vladimirgamalyan/imalive/include/config.example.h

#pragma once

// Copy this file to config.h and fill in your values.
// config.h is gitignored and must never be committed (see .gitignore / ADR-0003).

// --- WiFi ---
#define WIFI_SSID      "your-wifi-ssid"
#define WIFI_PASSWORD  "your-wifi-password"

// --- Telegram ---
// Bot token from @BotFather.
#define TG_BOT_TOKEN   "123456789:ABCdefGhIJKlmNoPQRstuVWxyz"
// Destination chat: a personal chat (positive numeric id) or a channel
// ("-100..." or "@channel"). For a channel, add the bot as an administrator
// with post permission. Prefer the numeric "-100..." form: a "@channel" username
// resolves only while the channel is public, and making it private drops the
// username, after which every API call fails with "chat not found". To find the
// numeric id, forward a channel post to @userinfobot.
#define TG_CHAT_ID     "123456789"
// User IDs allowed to send commands (/status, /mute, /unmute). Commands from any
// other sender are ignored. At least one id is required. Find yours via
// @userinfobot. Braces required, e.g. { 111, 222 }.
#define TG_ADMIN_IDS   { 123456789 }

// --- Behaviour ---
#define DEVICE_NAME    ""      // optional label shown in the message, e.g. "Cottage"
#define HEARTBEAT_MIN  5      // heartbeat interval, minutes
// Phase-lock heartbeat edits to round wall-clock times (e.g. :00, :05, :10 for a
// 5-minute interval) so "Last seen" values land on a tidy grid. Applies only when
// HEARTBEAT_MIN divides 60 evenly (5/10/15/20/30/60); ignored otherwise. Set to 0
// to keep edits at a fixed offset from power-on instead.
#define HEARTBEAT_ALIGN 1      // 1 = align to round minutes, 0 = off

// --- Timezone (POSIX TZ string, DST-aware; see CONCEPT.md "Time source") ---
// Asia/Bangkok, UTC+7, no DST.
#define TZ_STRING      "ICT-7"
